Smengerl/matrix_display/homeassistant_device_control_panel.jpg

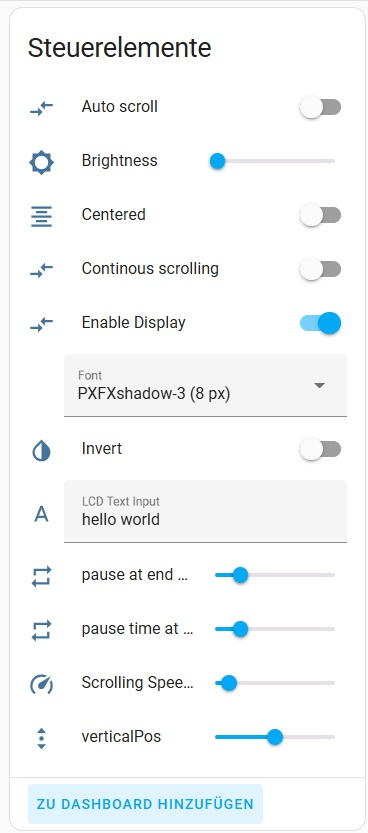
homeassistant_device_control_panel.jpg
